profdc9/VNA/board-smt/VNA board.png

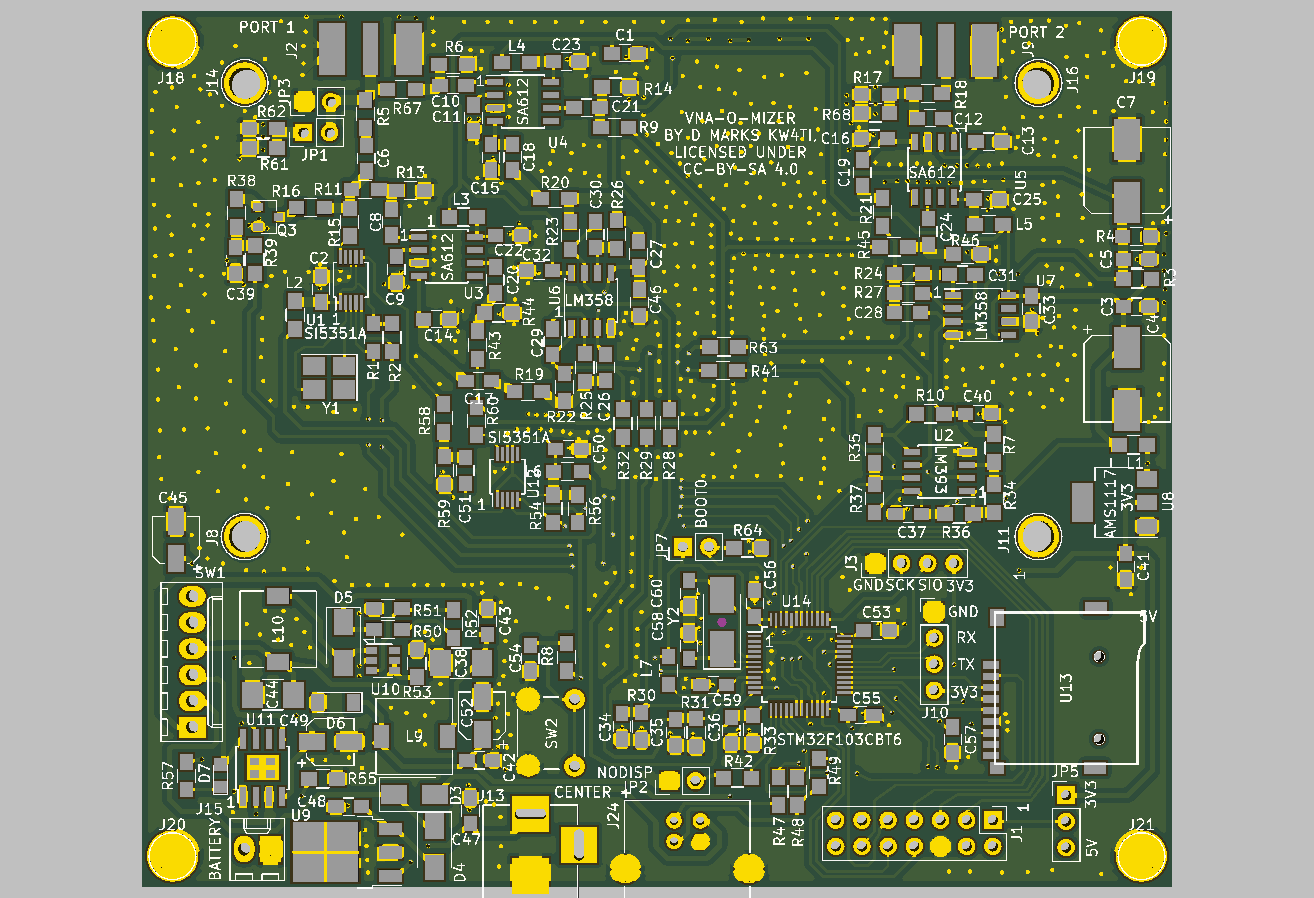
board-smt/VNA board.png
