profdc9/VNA/board/VNA board.png

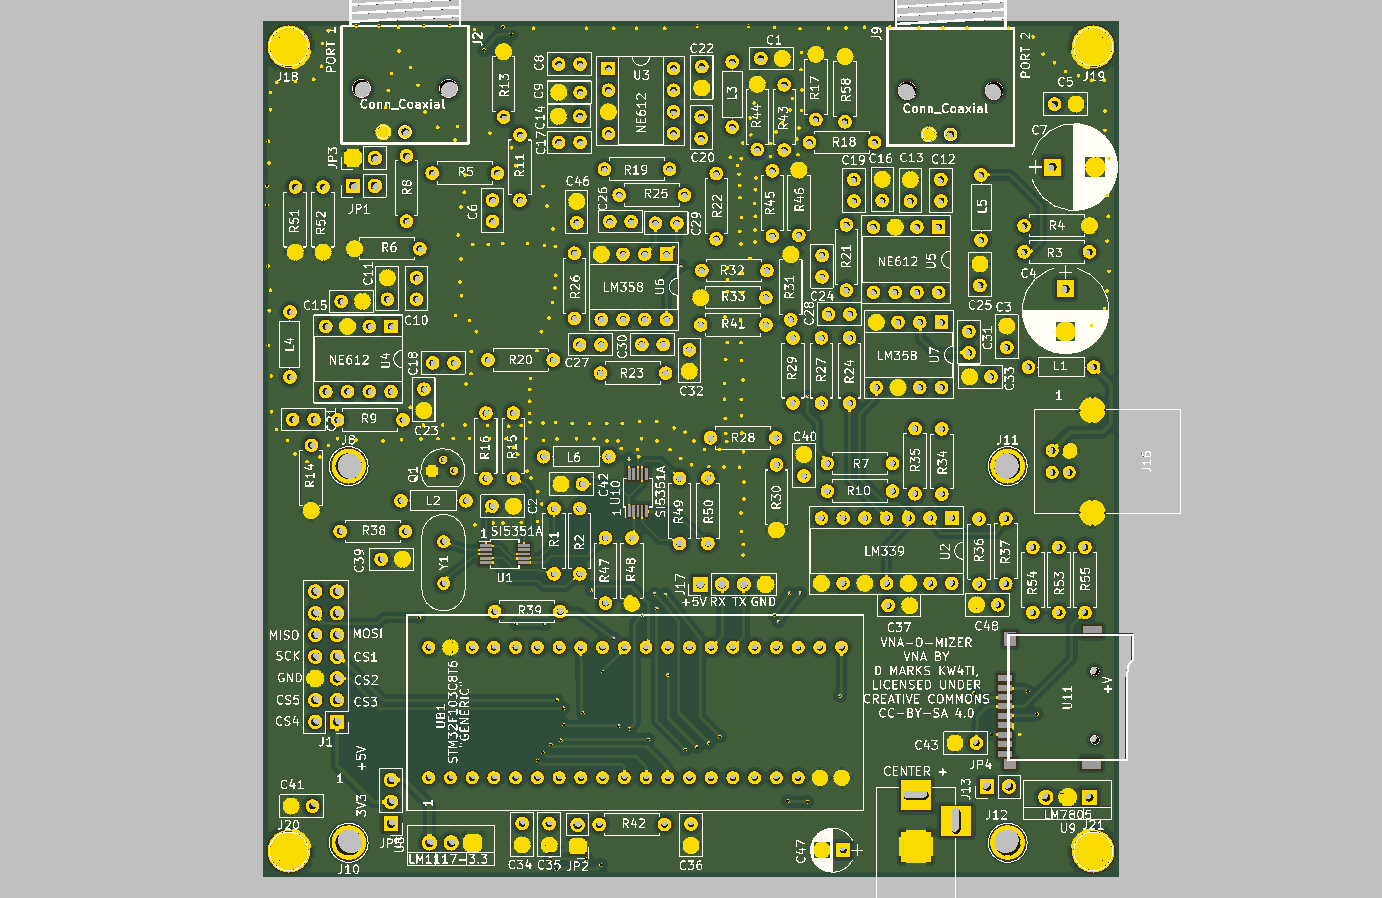
board/VNA board.png
