profdc9/VNA/daughterboard/daughterboard.png

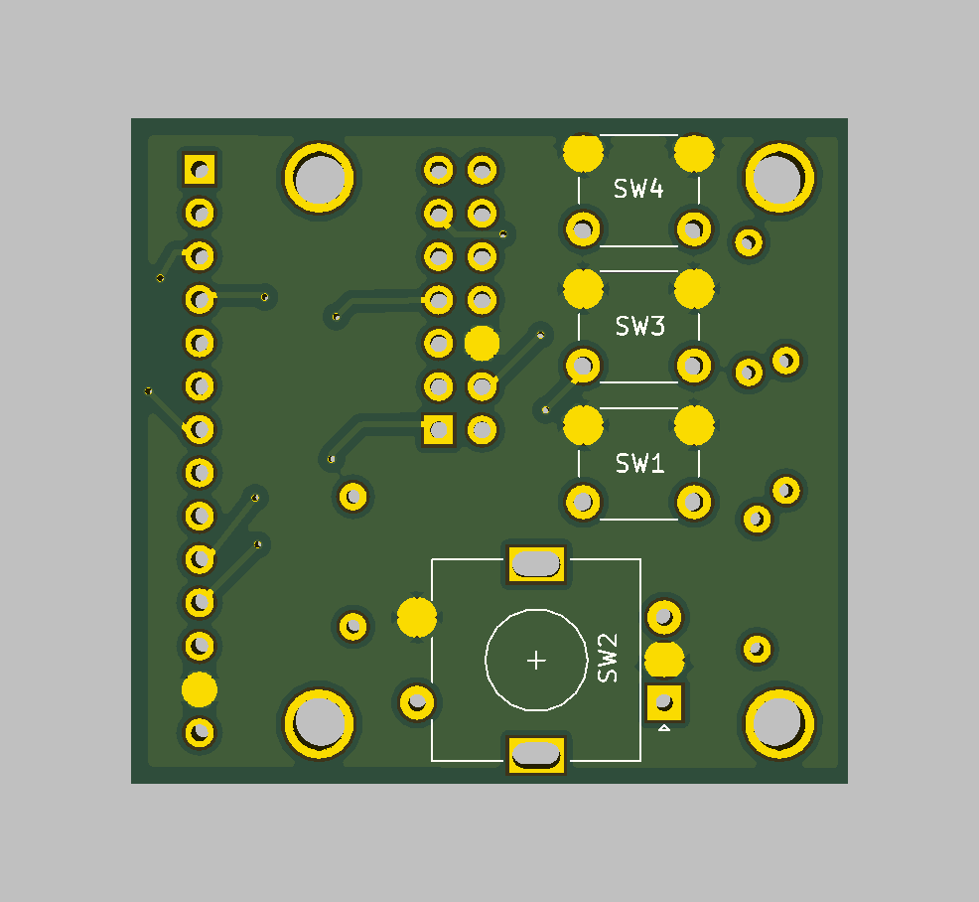
daughterboard/daughterboard.png
