profdc9/VNA/doc/vna-main-screen.jpg

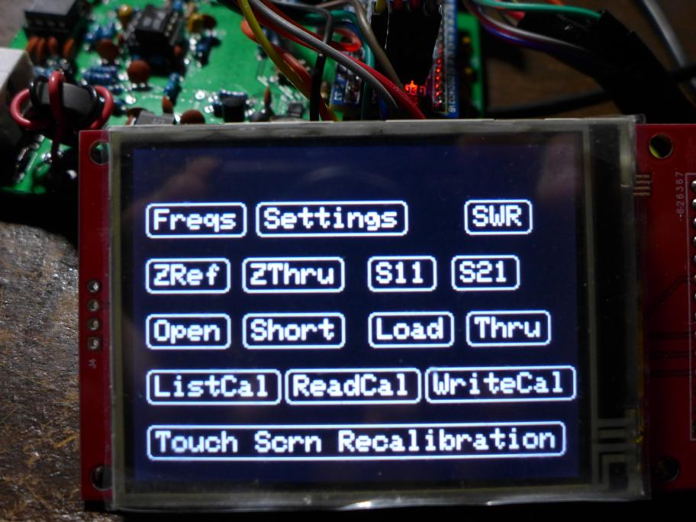
doc/vna-main-screen.jpg
