profdc9/VNA/fixture/fixture.png

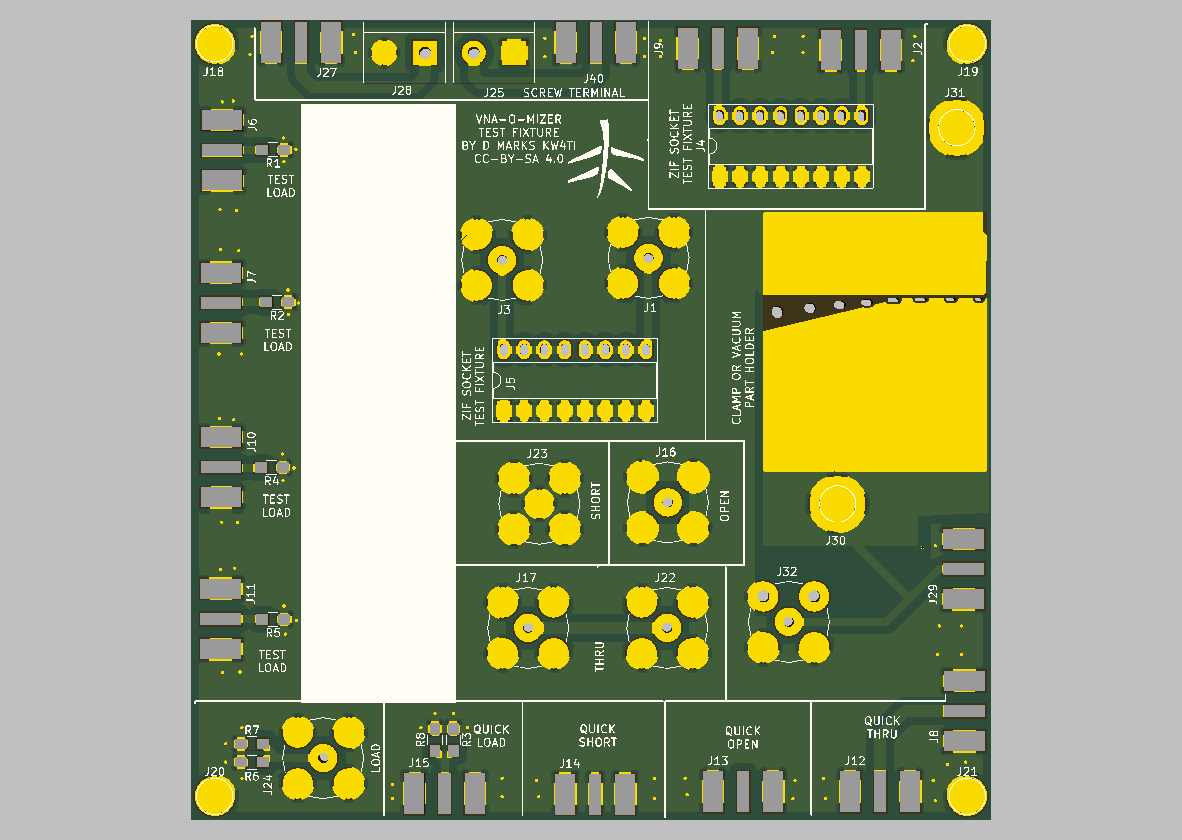
fixture/fixture.png
